michaelwittner/2526_5AHEL_LA_Schreibtischlampe/04_Verdrahtung/Bilder/Anschluss_Led-Einheit.jpeg

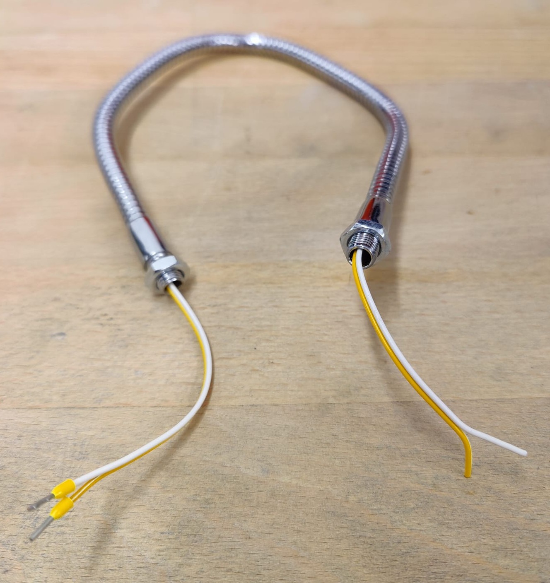
04_Verdrahtung/Bilder/Anschluss_Led-Einheit.jpeg
