michaelwittner/2526_5AHEL_LA_Schreibtischlampe/05_Protokol/Bilder/Breadboard_Schaltungen/CD4017_Breakoutboard.png

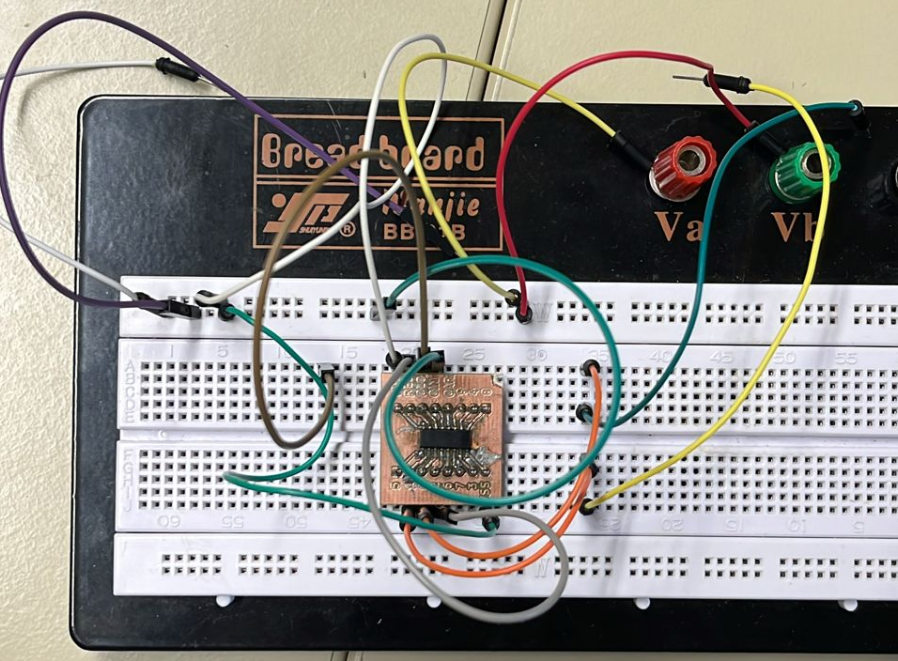
05_Protokol/Bilder/Breadboard_Schaltungen/CD4017_Breakoutboard.png
