michaelwittner/2526_5AHEL_LA_Schreibtischlampe/05_Protokol/Bilder/Breadboard_Schaltungen/LEDSchaltung2.png

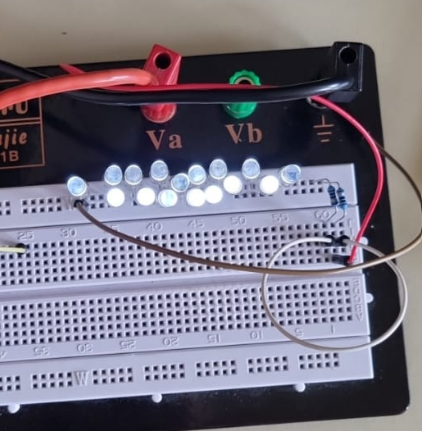
05_Protokol/Bilder/Breadboard_Schaltungen/LEDSchaltung2.png
