michaelwittner/2526_5AHEL_LA_Schreibtischlampe/05_Protokol/Bilder/Breadboard_Schaltungen/Schaltplan_Vorlage.png

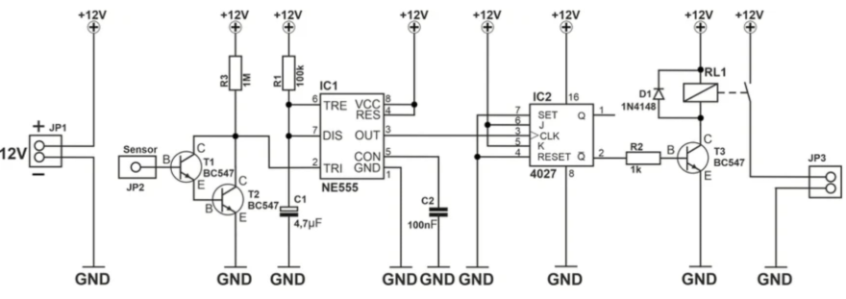
05_Protokol/Bilder/Breadboard_Schaltungen/Schaltplan_Vorlage.png
