michaelwittner/2526_5AHEL_LA_Schreibtischlampe/Bilder/Plakat.jpeg

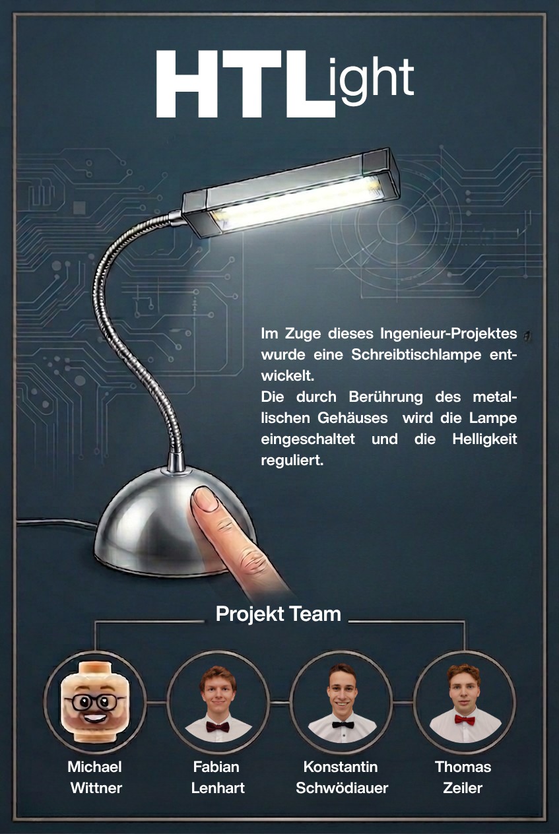
Bilder/Plakat.jpeg
